BBBSnowball/analog-noise/firmware/test1/src/lib.rs

#![no_std]

extern crate panic_halt;
extern crate cortex_m;
extern crate cortex_m_rt;
extern crate rtt_target;
pub extern crate stm32f0xx_hal;
extern crate usb_device;
extern crate usbd_serial;
extern crate ssd1680;
extern crate embedded_hal;
//extern crate embedded_hal_old;
extern crate embedded_hal_bus;
extern crate embedded_graphics;

extern crate portable_atomic;

pub use stm32f0xx_hal as hal;
pub use stm32f0xx_hal::pac as pac;

pub mod bootloader;
pub mod dac;
pub mod epd;
pub mod ims;
pub mod spi;
pub mod touch;
pub mod usb_serial;
